BennettRand/Dr-Wattson/software/daemon/data_demo.PNG

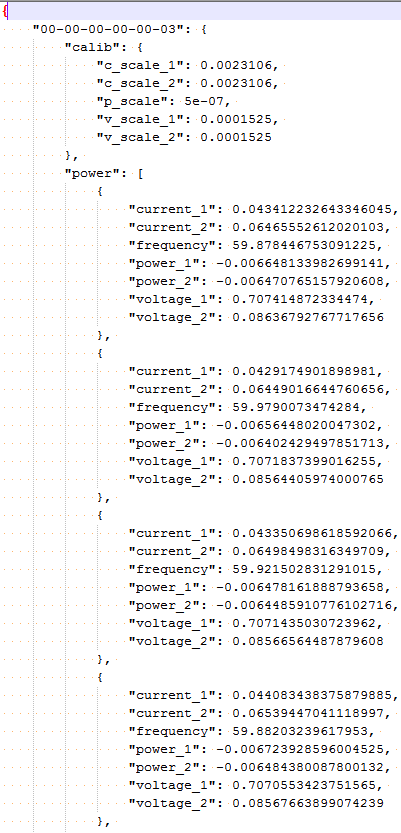
software/daemon/data_demo.PNG
