BennettRand/Dr-Wattson/hardware/firmware/baseStationFirmware/config.h

#ifndef _CONFIG_H_
#define _CONFIG_H_

/* file: config.h
 * This file provides the configuration provides the configuration definitions
 * for the Atmel Lightweight Mesh stack. The majority of these parameters are
 * compiled into the stack library at compile time, although a few are used by
 * the application program as well.
 */

#define USART_TX_vect USART1_TX_vect
#define USART_RX_vect USART1_RX_vect
#define USART_UDR     UDR1
#define USART_UBRR    UBRR1
#define USART_UCSRA   UCSR1A
#define USART_UCSRB   UCSR1B
#define USART_UCSRC   UCSR1C

#define APP_ENDPOINT              1

#define APP_CHANNEL             0x08i

#define APP_SECURITY_KEY          ((uint8_t*) "Dr.Wattson Key 0")
#define SYS_SECURITY_MODE                   0

#define NWK_BUFFERS_AMOUNT                  32
#define NWK_DUPLICATE_REJECTION_TABLE_SIZE  32
#define NWK_DUPLICATE_REJECTION_TTL         100 // ms
#define NWK_ROUTE_TABLE_SIZE                100
#define NWK_ROUTE_DEFAULT_SCORE             3
#define NWK_ACK_WAIT_TIME                   200 // ms

#define NWK_ENABLE_ROUTING
//#define NWK_ENABLE_SECURITY

#endif // _CONFIG_H_
